tlon-citizen/HapBand/3DModel/HapFingers-Thumb/TopSliderHR.stl

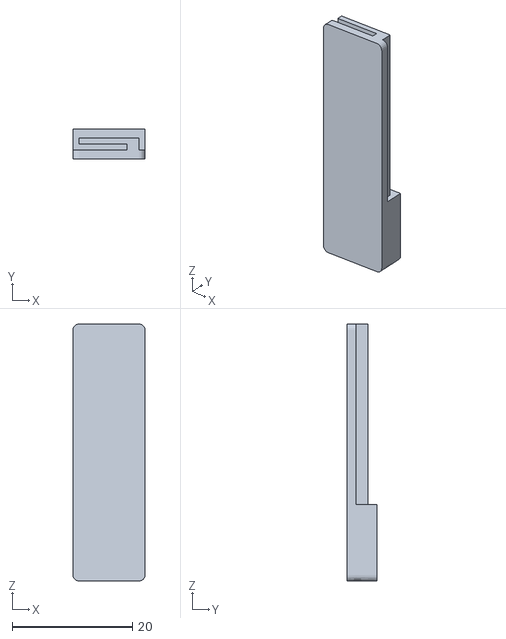
[picture p15: CAD file, 2020-12-28]
3DModel/HapFingers-Thumb/TopSliderHR.stl
12.0 x 4.95 x 42.8
