tlon-citizen/HapBand/3DModel/HapFingers-Index/FingerTipSupport.stl

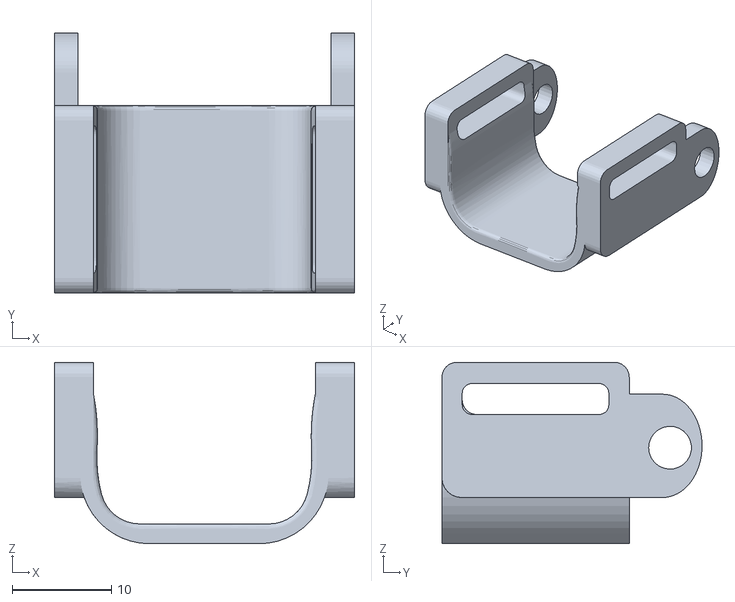
[picture p16: CAD file, 2020-12-28]
3DModel/HapFingers-Index/FingerTipSupport.stl
30.3 x 26.3 x 18.3
