tlon-citizen/HapBand/3DModel/HapFingers-Index/BottomSliderHR.stl

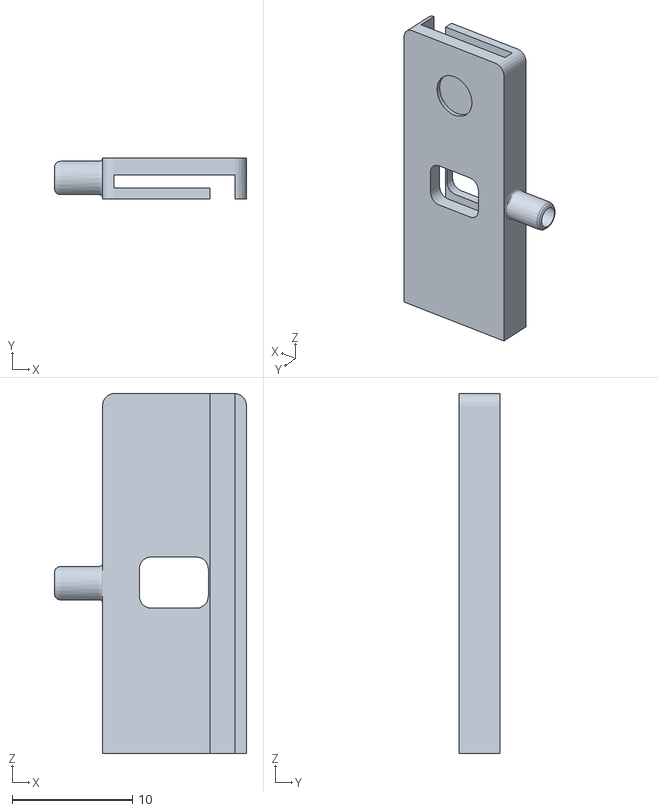
[picture p17: CAD file, 2020-12-28]
3DModel/HapFingers-Index/BottomSliderHR.stl
16.0 x 3.40 x 30.0
