tlon-citizen/HapBand/3DModel/HapFingers-Index/RampHR.stl

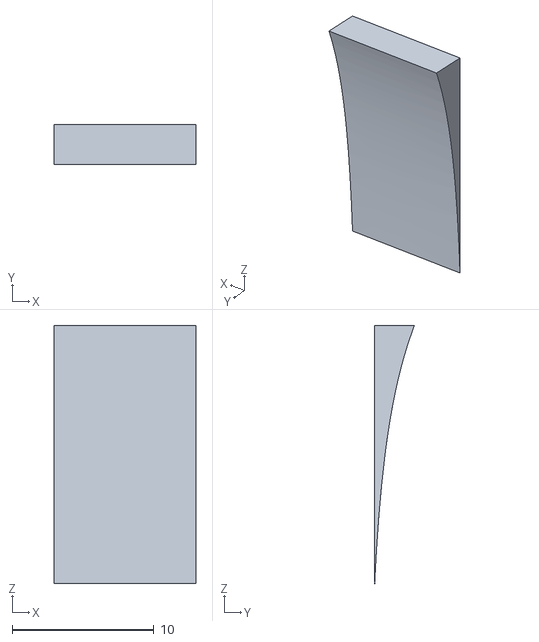
[picture p18: CAD file, 2020-12-28]
3DModel/HapFingers-Index/RampHR.stl
10.0 x 2.80 x 18.2
